bosco-drg/Analog-Compressor-Pedal/doc/AdaptationEntree1.png

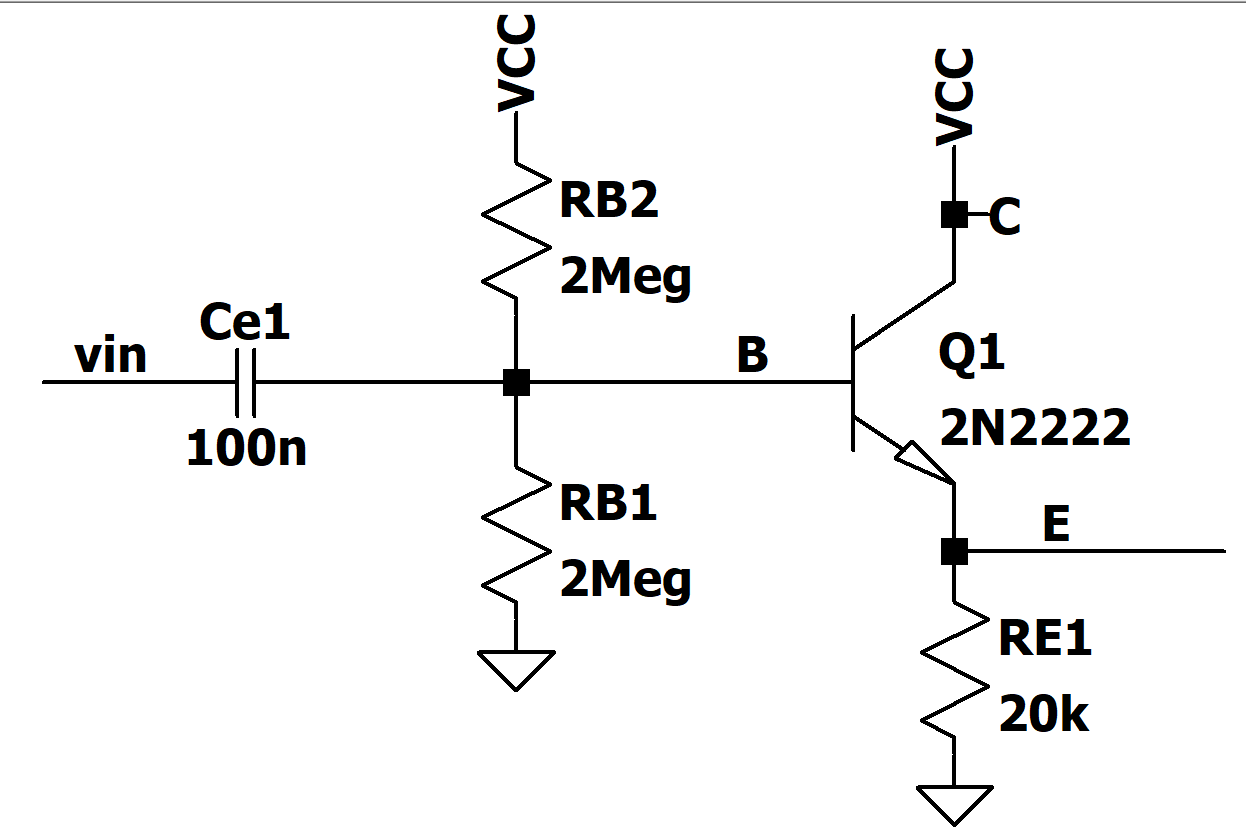
doc/AdaptationEntree1.png
