bosco-drg/Analog-Compressor-Pedal/doc/AdaptationEntree_petit_signaux.png

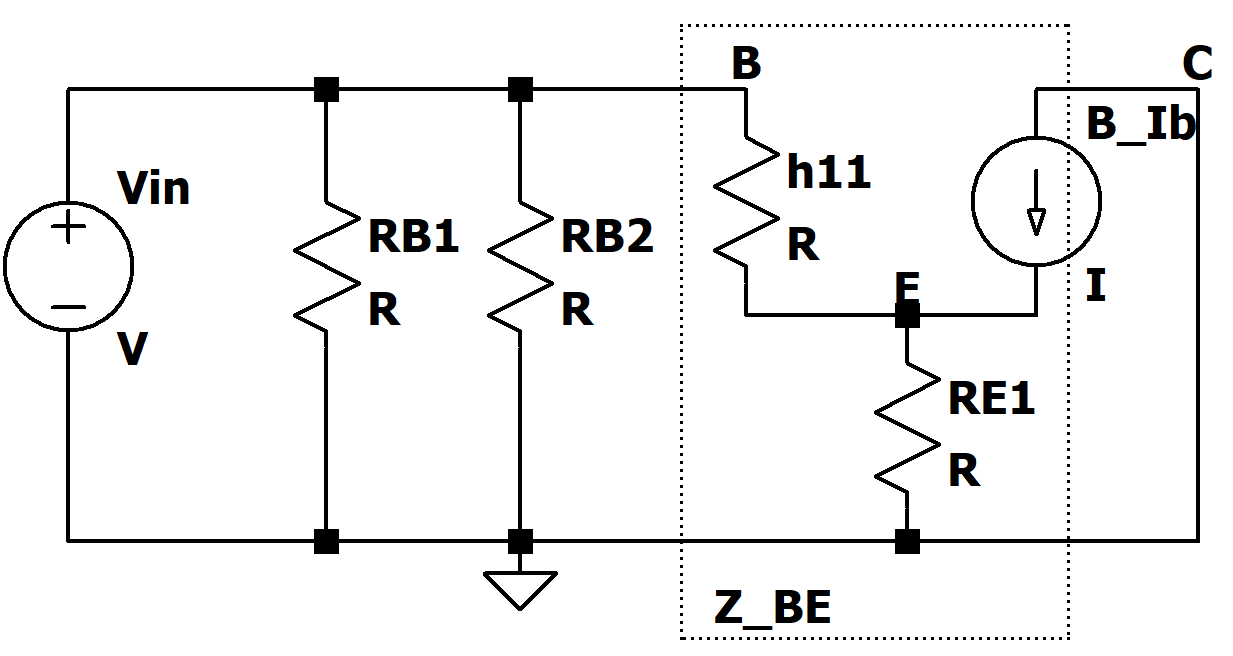
doc/AdaptationEntree_petit_signaux.png
