bosco-drg/Analog-Compressor-Pedal/doc/LTspice demo ampli enveloppe.png

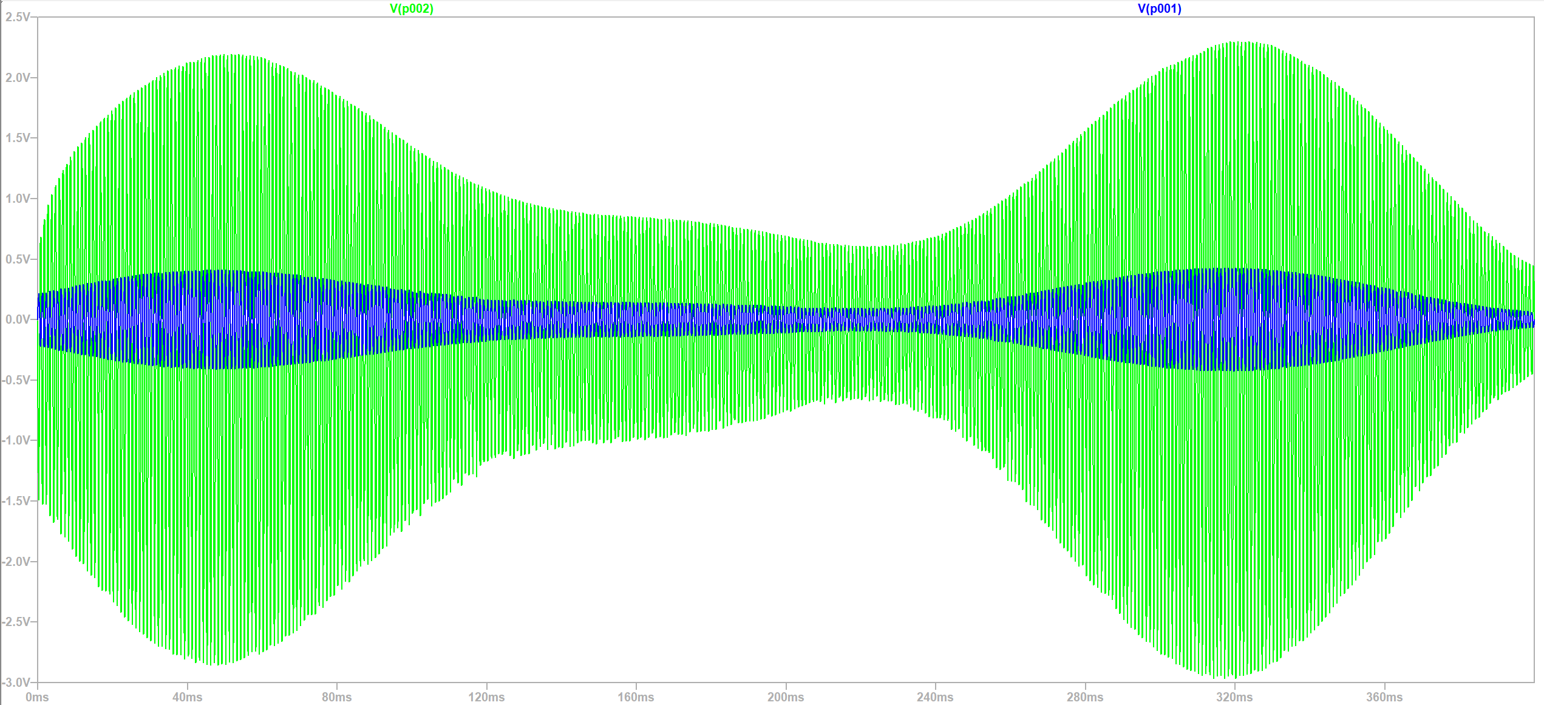
doc/LTspice demo ampli enveloppe.png
