bosco-drg/Analog-Compressor-Pedal/doc/Seuil_gain.png

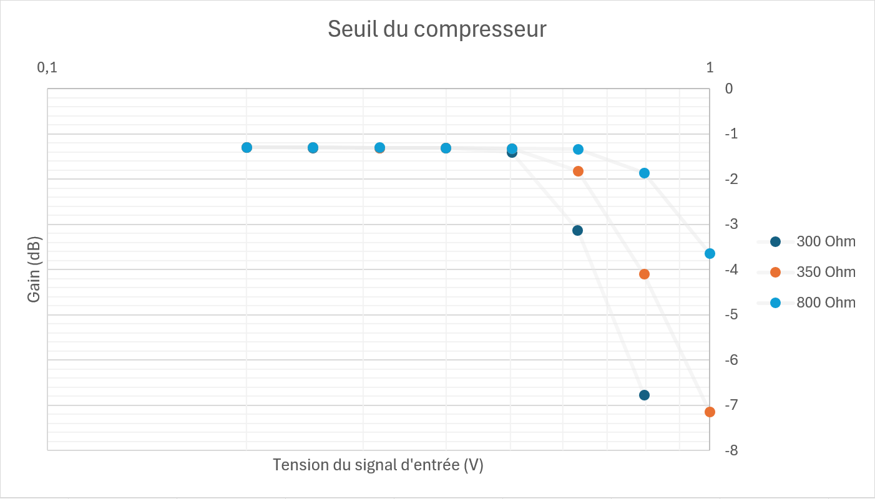
doc/Seuil_gain.png
