bosco-drg/Analog-Compressor-Pedal/LTSpice/Audio Tests/AUDIO_TEST_Circuit.asc

Amp1: res; 500k
C1: cap; 10n
C2: cap; 10µ
C3: cap; 100µ
C4: cap; 470n
C5: cap; 30µ
C6: cap; 10µ
Ce1: cap; 100n
Ce2: cap; 0.022µ
Cs1: cap; 0.47µ
D1: diode; 1N4148
J1: njf; 2N4117
Q1: npn; 2N2222
Q2: npn; 2N2222
Q3: npn; 2N2222
Q4: npn; 2N2222
R1: res; 20k
R2: res; 1k
R3: res; 1Meg
R4: res; 300k
R5: res; 3k
R6: res; 48k
R7: res; 6.5k
R8: res; 47k
R9: res; 1.5k
R10: res; 300
R11: res; 60
RB1: res; 1Meg
RB2: res; 1Meg
RB3: res; 1Meg
RB4: res; 1Meg
RB5: res; 124k
RB6: res; 10k
RC1: res; 1.1k
RE1: res; 20k
RE2: res; 20k
RE3: res; 1k
V1: voltage; 15
V2: voltage; 15
V3: voltage; PWL file=Audio_200mVpp.pwl
Named nets: 0, INPUT, Vout, VCC, Vcrtl, -VCC, Vin, Output, VC
.tran 0 5.5 1u
Ze ~ 400k
Zs ~ 180
Amp de Guitar
Ze = 400k
R11 potentiomètre pour controller la force de l'effet
100 ohm = effet fort
300 ohm = effet faible
500 ohm = pas d'effet
.wave "LTaudio_In.wav" 16 44.1k V(INPUT)
.wave "LTaudio_OUT.wav" 16 44.1k V(Output)
RC1 - Potentiomètre
Entre 1k - 2k qui correspond ~directement au gain
Son de guitare
PWL file=Audio_200mVpp.pwl 
Step - attaque en tension
BV1 Vin 0 V = (time < 50m ? 0.01 : 0.05)*sin(2*pi*1000*time)
