bosco-drg/Analog-Compressor-Pedal/LTSpice/Circuit Test Results/Common_Emitter_Test.asc

C1: cap; 10µ
Cs1: cap; 0.47µ
Q1: npn; 2N2222
R: res; {R}
RB1: res; 124k
RB2: res; 10k
RE1: res; 1k
RL: res; 500k
V1: voltage; ""; AC 1
V2: voltage; 15
Named nets: Output, 0, VCC, B, C, E
RC1 potentiomètre de 1k à 2kohm
RC potentiomètre 
de 1k à 2kohm
.step param R 1k 2k 100
.meas AC stage_gain MAX MAG(V(Output)/V(N001))
.ac lin 100 1k 20k
