bosco-drg/Analog-Compressor-Pedal/LTSpice/Circuit Test Results/Emmitter_Follower_Test.asc

B_Ib: current
Ce1: cap; 100n
h11: res
Q1: npn; 2N2222
RB1: res
RB1: res; 2Meg
RB2: res
RB2: res; 2Meg
RE1: res
RE1: res; 20k
V1: voltage; 15
Vin: voltage
Vin: voltage; ""; AC 1
Named nets: 0, VCC, vin, B, C, E
.ac dec 100 10 1Meg
Z_BE
