bosco-drg/Analog-Compressor-Pedal/LTSpice/Circuit_complet_avec_Adaptation.asc

Amp1: res; 500k
C1: cap; 20µ
C2: cap; 10µ
C3: cap; 100µ
C4: cap; 470n
C7: cap; 10µ
Ce1: cap; 100n
Ce2: cap; 0.022µ
Cs2: cap; 0.47µ
D1: diode; 1N4148
J1: njf; 2N4117
Q1: npn; 2N2222
Q2: npn; 2N2222
Q3: npn; 2N2222
Q4: npn; 2N2222
R1: res; 21k
R2: res; 1k
R3: res; 1Meg
R4: res; 300k
R5: res; 2.5k
R6: res; 39k
R7: res; 6.2k
R8: res; 47k
R9: res; 100
R10: res; 400
RB1: res; 2Meg
RB2: res; 2Meg
RB3: res; 2Meg
RB4: res; 2Meg
RB5: res; 124k
RB6: res; 10k
RC1: res; 1.2k
RE1: res; 20k
RE2: res; 20k
RE3: res; 1k
V1: voltage; V = (0.22*(1 + 0.7*sin(2*pi*4*time) + 0.3*sin(2*pi*7*time)))*sin(2*pi*1000*time)
V2: voltage; 15
V3: voltage; 15
Named nets: 0, INPUT, Vout, VCC, Vcrtl, -VCC, Vin, Output, VC
.tran 0 400m 1u
Zin ~ 800k
Amp de Guitar
Gain ~ 2
phase shift of 0.3ms
Ze = 800k
On peut magouiller avec C6 et C7 qui change un peu le "phase shift" et le gain
R10 potentiomètre pour controller la force de l'effet
300 ohm = effet fort
450 ohm = effet ok
800 ohm = pas d'effet
.wave "LT_In.wav" 16 44.1k V(INPUT)
.wave "LT_OUT.wav" 16 44.1k V(Output)
RC1 potentiomètre de 1k à 2kohm
R1 potentiomètre de 21k à 1k
